Ilikemining1/MiniPhoneSwitch/Spice/ToneGeneration/ToneGenTest.asc

C1: cap; .1µ
C2: cap; .1µ
C3: cap; .1µ
C4: cap; .1µ
C5: cap; .1µ
C6: cap; .1µ
C7: cap; .1µ
C8: cap; .1µ
D1: diode; 1N4148
D2: diode; 1N4148
D3: diode; 1N4148
D4: diode; 1N4148
D5: diode; 1N4148
D6: diode; 1N4148
D7: diode; 1N4148
D8: diode; 1N4148
R1: res; 2.55k
R2: res; 2.55k
R3: res; 4.7k
R4: res; 2.34k
R5: res; 3.32k
R6: res; 3.32k
R7: res; 4.7k
R8: res; 2.34k
R9: res; 100k
R11: res; 1Meg
R12: res; 270k
R13: res; 3.6k
R14: res; 3.6k
R15: res; 4.7k
R16: res; 2.34k
R17: res; 100k
R18: res; 4.53k
R19: res; 4.53k
R20: res; 4.7k
R21: res; 2.34k
S1: sw; BusySignal
U1: TL074
U2: TL074
U3: TL074
U4: TL074
U5: TL074
V1: voltage; 5; Rser=1
V2: voltage; 5; Rser=1
V3: voltage; 5; Rser=1
V4: voltage; 5; Rser=1
V5: voltage; PULSE(0 1 0 10u 10u .25 .5 12)
V6: voltage; 5; Rser=1
V7: voltage; 5; Rser=1
V8: voltage; 5; Rser=1
V9: voltage; 5; Rser=1
Named nets: 0
.lib TL074.lib
.tran 0 6 1 startup uic
.wave reorder.wav 16 8k V(n023)
.model BusySignal SW(Ron=1 Roff=100Gig Vt=.5 Vh=-.4)
