Ilikemining1/MiniPhoneSwitch/Spice/RingGen.asc

C5: cap; 2.2µ
C6: cap; 2.2µ
D5: diode; 1N4148
D6: diode; 1N4148
R1: res; 1k
R13: res; 3.6k
R14: res; 3.6k
R15: res; 4.7k
R16: res; 2.2k
U4: TL074
V6: voltage; 5; Rser=1
V7: voltage; 5; Rser=1
Named nets: 0
.lib TL074.lib
.tran 0 100 1 startup uic
