Ilikemining1/MiniPhoneSwitch/Spice/PhoneInterfaceGyratorsTransient.asc

C1: cap; 3.3µ
C2: cap; 3.3µ
C3: cap; 8µ
C4: cap; 2.2µ
C5: cap; 2.2µ
D1: diode; 1N4148
D2: diode; 1N4148
D3: diode; 1N4148
D4: zener; BZX84B9V1L
D6: zener; BZX84B9V1L
R1: res; 6.8k
R2: res; 6.8k
R3: res; 200
R4: res; 6.8k
R5: res; 6.8k
R6: res; 200
R7: res; 4.7k
R8: res; 1k
R9: res; 6930
R10: res; 33k
R11: res; 33k
R12: res; 100
U1: PHPT61003PY
U2: PHPT61003NY
U3: TCMD1000
V1: voltage; 48; Rser=.1
V3: voltage; 3.3v
V4: voltage; SINE(0 127 20)
Named nets: 0
.tran 0 1 10m
.model PhoneHook SW(Ron=10 Roff=10Meg Vt=4.5 Vh=-.4)
