Ilikemining1/MiniPhoneSwitch/Spice/PhoneInterfaceGyratorsFreqCurrentBode.asc

C1: cap; 3.3µ
C2: cap; 3.3µ
C3: cap; 2.2µ
C4: cap; 2.2µ
D1: diode; 1N4148
D2: diode; 1N4148
D3: zener; BZX84B9V1L
D4: zener; BZX84B9V1L
R1: res; 6.8k
R2: res; 6.8k
R3: res; 200
R4: res; 6.8k
R5: res; 6.8k
R6: res; 200
R7: res; 10
U1: PHPT61003PY
U2: PHPT61003NY
V1: voltage; 48; Rser=.1
V2: voltage; ""; AC 1
Named nets: 0
.lib PHPT61003NY.lib
.ac dec 25 1 3500
.lib PHPT61003PY.lib
