Ilikemining1/MiniPhoneSwitch/Spice/PhoneInterfaceGyratorNPN.asc

C1: cap; 3.9µ
D1: diode; 1N4148
R1: res; 6.8k
R2: res; 6.8k
R3: res; 200
R4: res; 1
U1: PHPT61003NY
V1: voltage; 48; Rser=.1
V2: voltage; ""; AC 10
Named nets: 0
.lib PHPT61003NY.lib
.ac dec 25 1 300
